ProxyPlayerHD/65816_SBC_v1/KiCad/65C816_SBC.kicad_sch

## KiCad design KiCad/65C816_SBC.kicad_sch (2022-10-29)

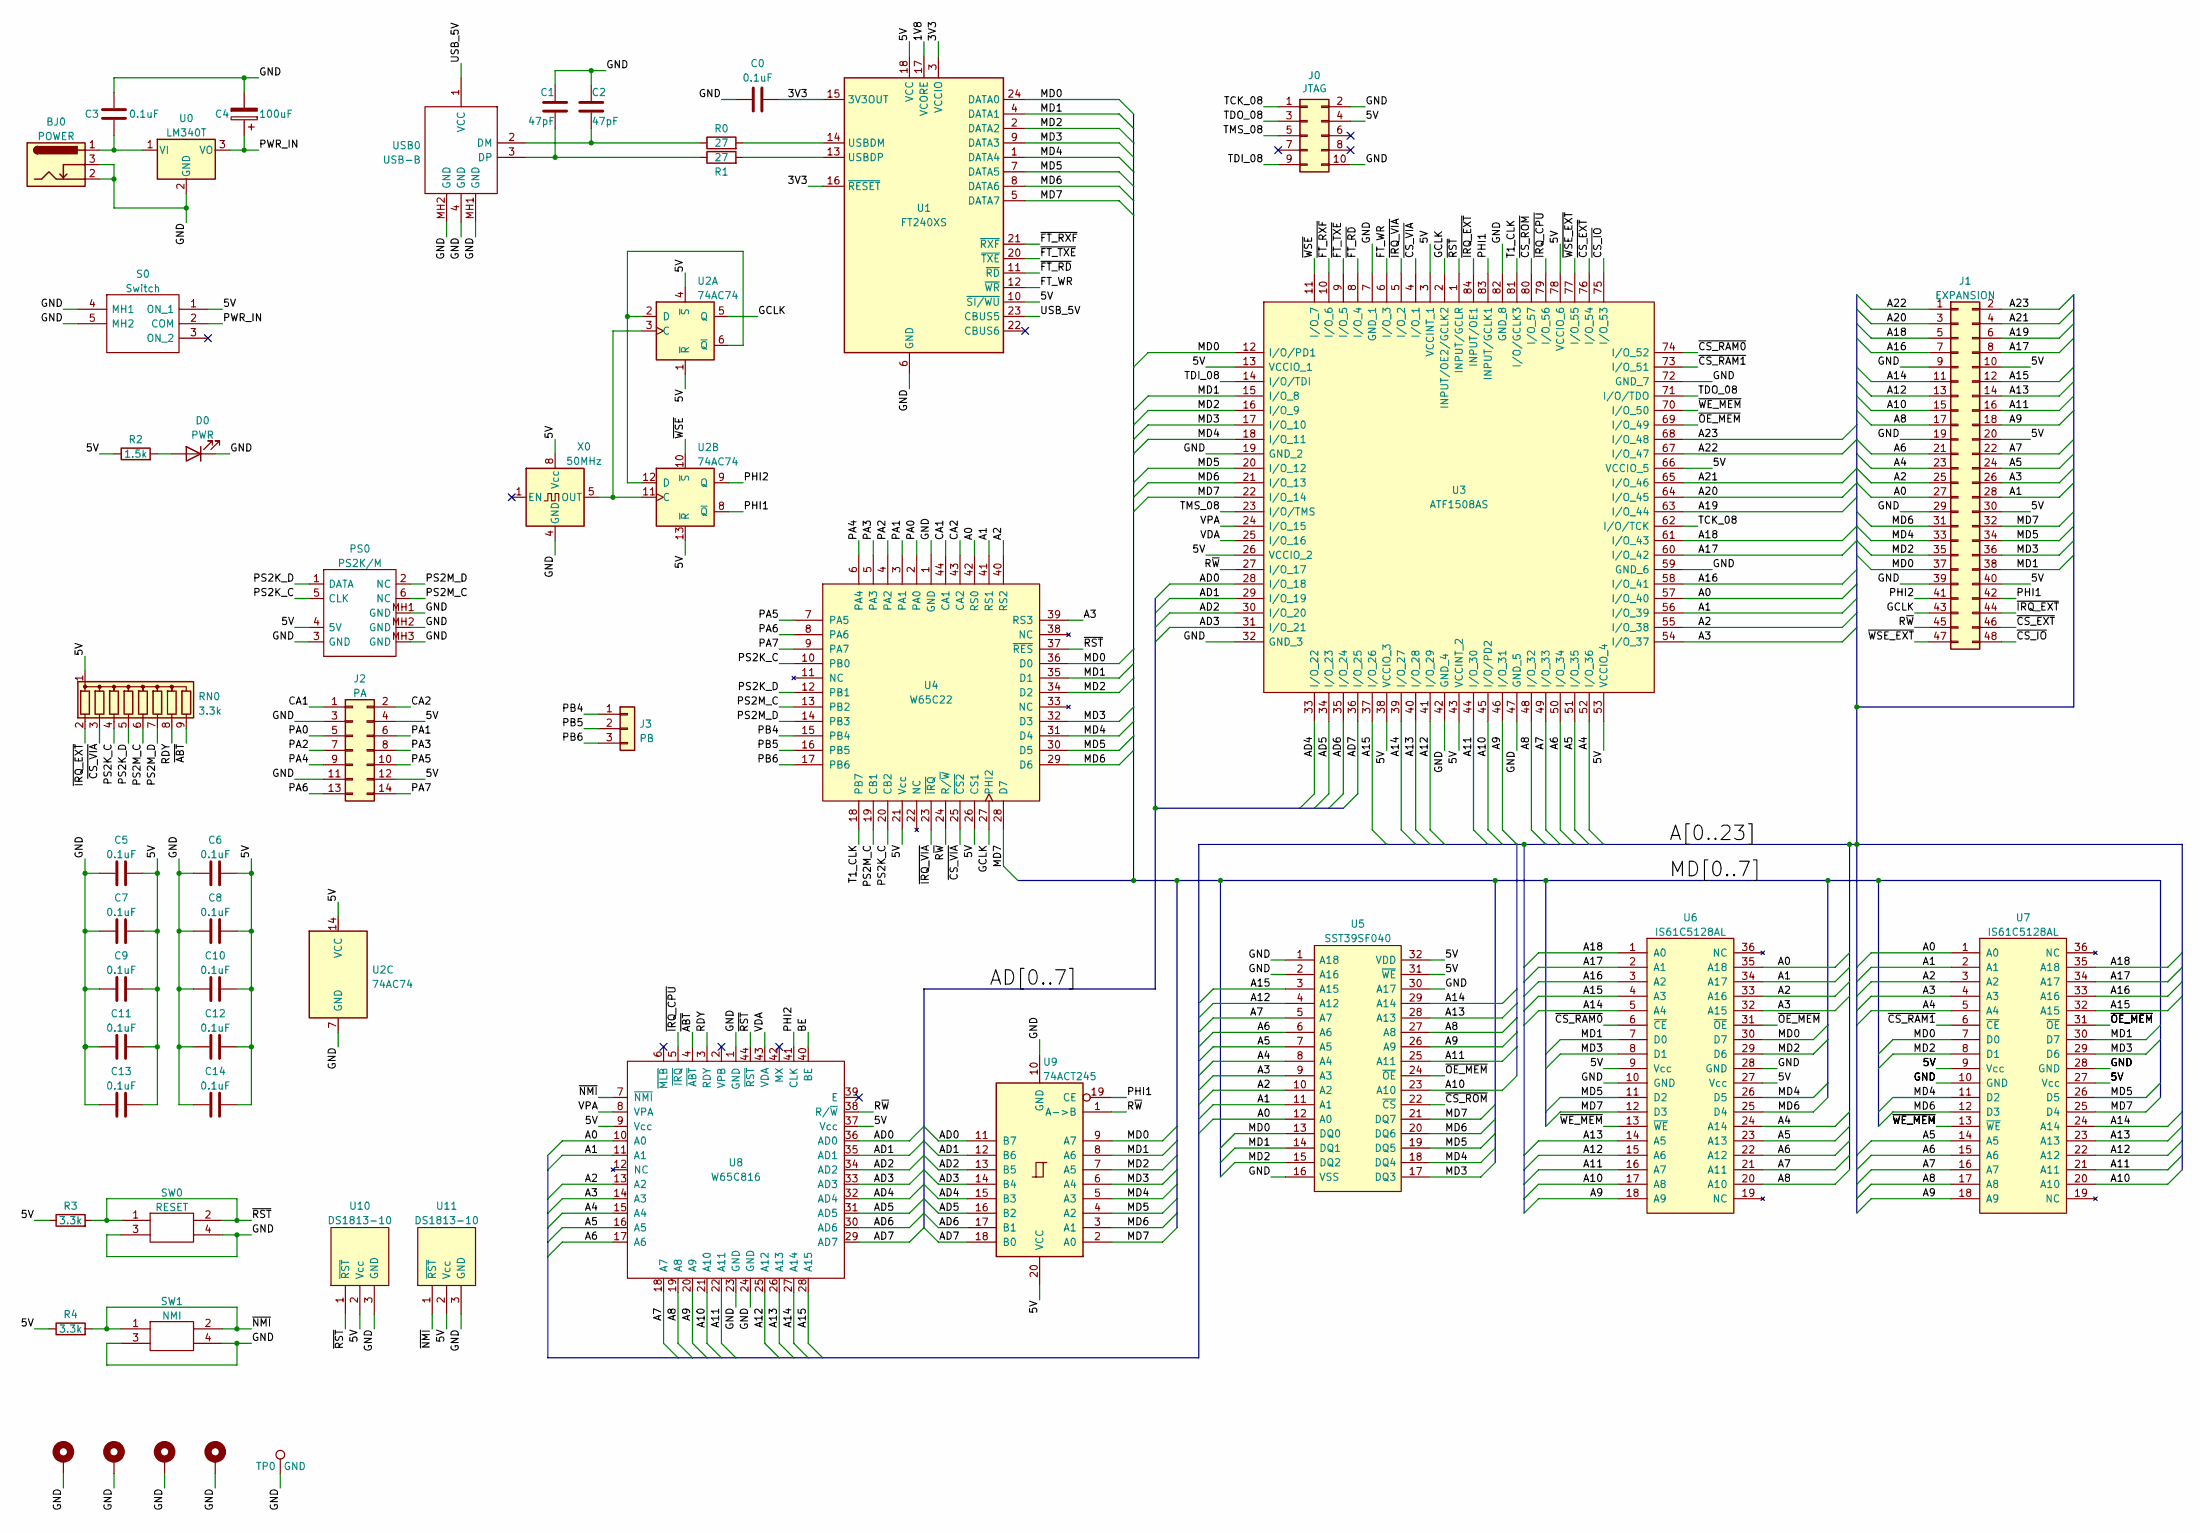
[picture p2: schematic 65C816_SBC.kicad_sch]

Parts:
BJ0: POWER; BarrelJack_Horizontal
C0, C3, C5, C6, C7, C8, C9, C10, C11, C12, C13, C14: 0.1uF; C_Disc_D4.3mm_W1.9mm_P5.00mm
C1, C2: 47pF; C_Disc_D4.3mm_W1.9mm_P5.00mm
C4: 100uF; CP_Radial_D4.0mm_P2.00mm
D0: PWR; LED_D4.0mm
H0, H1, H2, H3: H; MountingHole_3.2mm_M3_Pad
J0: JTAG; PinHeader_2x05_P2.54mm_Vertical
J1: EXPANSION; PinHeader_2x24_P2.54mm_Vertical
J2: PA; PinHeader_2x07_P2.54mm_Vertical
J3: PB; PinHeader_1x03_P2.54mm_Vertical
PS0: PS2K/M; PS2; Mouser Part Number 571-5749266-1
R0, R1: 27; R_Axial_DIN0207_L6.3mm_D2.5mm_P2.54mm_Vertical
R2: 1.5k; R_Axial_DIN0207_L6.3mm_D2.5mm_P2.54mm_Vertical
R3, R4: 3.3k; R_Axial_DIN0207_L6.3mm_D2.5mm_P2.54mm_Vertical
RN0: 3.3k; R_Array_SIP9
S0: Switch; Mouser Part Number 688-SSSF012100
SW0: RESET; button
SW1: NMI; button
TP0: GND; TestPoint_Bridge_Pitch5.08mm_Drill1.3mm
U0: LM340T; TO-220-3_Vertical
U1: FT240XS; SSOP-24_3.9x8.7mm_P0.635mm
U2: 74AC74; DIP-14_W7.62mm_Socket
U3: ATF1508AS; PLCC-84_THT-Socket
U4: W65C22; PLCC-44_THT-Socket
U5: SST39SF040; PLCC-32_THT-Socket
U6, U7: IS61C5128AL; SOJ-36_10.16x23.49mm_P1.27mm
U8: W65C816; PLCC-44_THT-Socket
U9: 74ACT245; DIP-20_W7.62mm_Socket
U10, U11: DS1813-10; TO-92L_Inline_Wide
USB0: USB-B; Mouser Part Number 523-UE27-BC54-130
X0: 50MHz; Oscillator_DIP-8

Connections:
1V8: U1.17 (VCORE)
3V3: C0.1, U1.3 (VCCIO), U1.15 (3V3OUT), U1.16 (~RESET)
5V: C5.2, C6.2, C7.2, C8.2, C9.2, C10.2, C11.2, C12.2, C13.2, C14.2, J0.4, J1.10, J1.20, J1.30, J1.40, J2.4, J2.12, PS0.4 (5V), R2.1, R3.1, R4.1, RN0.1 (common), S0.1 (ON_1), U1.10 (~SI/WU), U1.18 (VCC), U2.1 (~R), U2.4 (~S), U2.13 (~R), U2.14 (VCC), U3.3 (VCCINT_1), U3.13 (VCCIO_1), U3.26 (VCCIO_2), U3.38 (VCCIO_3), U3.43 (VCCINT_2), U3.53 (VCCIO_4), U3.66 (VCCIO_5), U3.78 (VCCIO_6), U4.21 (Vcc), U4.26 (CS1), U5.31 (~WE), U5.32 (VDD), U6.9 (Vcc), U6.27 (Vcc), U7.9 (Vcc), U7.27 (Vcc), U8.9 (Vcc), U8.37 (Vcc), U9.20 (VCC), U10.2 (Vcc), U11.2 (Vcc), X0.8 (Vcc)
A0: J1.27, U3.57 (I/O_40), U4.42 (RS0), U5.12 (A0), U6.35 (A18), U7.1 (A0), U8.10 (A0)
A1: J1.28, U3.56 (I/O_39), U4.41 (RS1), U5.11 (A1), U6.34 (A17), U7.2 (A1), U8.11 (A1)
A2: J1.25, U3.55 (I/O_38), U4.40 (RS2), U5.10 (A2), U6.33 (A16), U7.3 (A2), U8.13 (A2)
A3: J1.26, U3.54 (I/O_37), U4.39 (RS3), U5.9 (A3), U6.32 (A15), U7.4 (A3), U8.14 (A3)
A4: J1.23, U3.52 (I/O_36), U5.8 (A4), U6.24 (A14), U7.5 (A4), U8.15 (A4)
A5: J1.24, U3.51 (I/O_35), U5.7 (A5), U6.23 (A13), U7.14 (A5), U8.16 (A5)
A6: J1.21, U3.50 (I/O_34), U5.6 (A6), U6.22 (A12), U7.15 (A6), U8.17 (A6)
A7: J1.22, U3.49 (I/O_33), U5.5 (A7), U6.21 (A11), U7.16 (A7), U8.18 (A7)
A8: J1.17, U3.48 (I/O_32), U5.27 (A8), U6.20 (A10), U7.17 (A8), U8.19 (A8)
A9: J1.18, U3.46 (I/O_31), U5.26 (A9), U6.18 (A9), U7.18 (A9), U8.20 (A9)
A10: J1.15, U3.45 (I/O/PD2), U5.23 (A10), U6.17 (A8), U7.20 (A10), U8.21 (A10)
A11: J1.16, U3.44 (I/O_30), U5.25 (A11), U6.16 (A7), U7.21 (A11), U8.22 (A11)
A12: J1.13, U3.41 (I/O_29), U5.4 (A12), U6.15 (A6), U7.22 (A12), U8.25 (A12)
A13: J1.14, U3.40 (I/O_28), U5.28 (A13), U6.14 (A5), U7.23 (A13), U8.26 (A13)
A14: J1.11, U3.39 (I/O_27), U5.29 (A14), U6.5 (A4), U7.24 (A14), U8.27 (A14)
A15: J1.12, U3.37 (I/O_26), U5.3 (A15), U6.4 (A3), U7.32 (A15), U8.28 (A15)
A16: J1.7, U3.58 (I/O_41), U6.3 (A2), U7.33 (A16)
A17: J1.8, U3.60 (I/O_42), U6.2 (A1), U7.34 (A17)
A18: J1.5, U3.61 (I/O_43), U6.1 (A0), U7.35 (A18)
A19: J1.6, U3.63 (I/O_44)
A20: J1.3, U3.64 (I/O_45)
A21: J1.4, U3.65 (I/O_46)
A22: J1.1, U3.67 (I/O_47)
A23: J1.2, U3.68 (I/O_48)
AD0: U3.28 (I/O_18), U8.36 (AD0), U9.11 (B7)
AD1: U3.29 (I/O_19), U8.35 (AD1), U9.12 (B6)
AD2: U3.30 (I/O_20), U8.34 (AD2), U9.13 (B5)
AD3: U3.31 (I/O_21), U8.33 (AD3), U9.14 (B4)
AD4: U3.33 (I/O_22), U8.32 (AD4), U9.15 (B3)
AD5: U3.34 (I/O_23), U8.31 (AD5), U9.16 (B2)
AD6: U3.35 (I/O_24), U8.30 (AD6), U9.17 (B1)
AD7: U3.36 (I/O_25), U8.29 (AD7), U9.18 (B0)
BE: U8.40 (BE)
CA1: J2.1, U4.44 (CA1)
CA2: J2.2, U4.43 (CA2)
FT_WR: U1.12 (~WR), U3.6 (I/O_3)
GCLK: J1.43, U2.5 (Q), U3.2 (INPUT/OE2/GCLK2), U4.27 (PHI2)
GND: BJ0.2, BJ0.3, C0.2, C1.2, C2.1, C3.2, C4.2, C5.1, C6.1, C7.1, C8.1, C9.1, C10.1, C11.1, C12.1, C13.1, C14.1, D0.1 (K), H0.1, H1.1, H2.1, H3.1, J0.2, J0.10, J1.9, J1.19, J1.29, J1.39, J2.3, J2.11, PS0.3 (GND), PS0.MH1 (GND), PS0.MH2 (GND), PS0.MH3 (GND), S0.4 (MH1), S0.5 (MH2), SW0.3, SW0.4, SW1.3, SW1.4, TP0.1, U0.2 (GND), U1.6 (GND), U1.19 (GND), U2.7 (GND), U3.7 (GND_1), U3.19 (GND_2), U3.32 (GND_3), U3.42 (GND_4), U3.47 (GND_5), U3.59 (GND_6), U3.72 (GND_7), U3.82 (GND_8), U4.1 (GND), U5.1 (A18), U5.2 (A16), U5.16 (VSS), U5.30 (A17), U6.10 (GND), U6.28 (GND), U7.10 (GND), U7.28 (GND), U8.1 (GND), U8.23 (GND), U8.24 (GND), U9.10 (GND), U10.3 (GND), U11.3 (GND), USB0.4 (GND), USB0.MH1 (GND), USB0.MH2 (GND), X0.4 (GND)
MD0: J1.37, U1.24 (DATA0), U3.12 (I/O/PD1), U4.36 (D0), U5.13 (DQ0), U6.30 (D7), U7.7 (D0), U9.9 (A7)
MD1: J1.38, U1.4 (DATA1), U3.15 (I/O_8), U4.35 (D1), U5.14 (DQ1), U6.7 (D0), U7.30 (D7), U9.8 (A6)
MD2: J1.35, U1.2 (DATA2), U3.16 (I/O_9), U4.34 (D2), U5.15 (DQ2), U6.29 (D6), U7.8 (D1), U9.7 (A5)
MD3: J1.36, U1.9 (DATA3), U3.17 (I/O_10), U4.32 (D3), U5.17 (DQ3), U6.8 (D1), U7.29 (D6), U9.6 (A4)
MD4: J1.33, U1.1 (DATA4), U3.18 (I/O_11), U4.31 (D4), U5.18 (DQ4), U6.26 (D5), U7.11 (D2), U9.5 (A3)
MD5: J1.34, U1.7 (DATA5), U3.20 (I/O_12), U4.30 (D5), U5.19 (DQ5), U6.11 (D2), U7.26 (D5), U9.4 (A2)
MD6: J1.31, U1.8 (DATA6), U3.21 (I/O_13), U4.29 (D6), U5.20 (DQ6), U6.25 (D4), U7.12 (D3), U9.3 (A1)
MD7: J1.32, U1.5 (DATA7), U3.22 (I/O_14), U4.28 (D7), U5.21 (DQ7), U6.12 (D3), U7.25 (D4), U9.2 (A0)
unnamed: BJ0.1, C3.1, U0.1 (VI)
unnamed: C1.1, R1.1, USB0.3 (DP)
unnamed: C2.2, R0.1, USB0.2 (DM)
unnamed: D0.2 (A), R2.2
unnamed: R0.2, U1.14 (USBDM)
unnamed: R1.2, U1.13 (USBDP)
unnamed: U2.3 (C), U2.11 (C), X0.5 (OUT)
unnamed: U2.2 (D), U2.6 (~Q), U2.12 (D)
PA0: J2.5, U4.2 (PA0)
PA1: J2.6, U4.3 (PA1)
PA2: J2.7, U4.4 (PA2)
PA3: J2.8, U4.5 (PA3)
PA4: J2.9, U4.6 (PA4)
PA5: J2.10, U4.7 (PA5)
PA6: J2.13, U4.8 (PA6)
PA7: J2.14, U4.9 (PA7)
PB4: J3.1, U4.15 (PB4)
PB5: J3.2, U4.16 (PB5)
PB6: J3.3, U4.17 (PB6)
PHI1: J1.42, U2.8 (~Q), U3.83 (INPUT/GCLK1), U9.19 (CE)
PHI2: J1.41, U2.9 (Q), U8.41 (CLK)
PS2K_C: PS0.5 (CLK), RN0.4 (R3), U4.10 (PB0), U4.20 (CB2)
PS2K_D: PS0.1 (DATA), RN0.5 (R4), U4.12 (PB1)
PS2M_C: PS0.6 (NC), RN0.6 (R5), U4.13 (PB2), U4.19 (CB1)
PS2M_D: PS0.2 (NC), RN0.7 (R6), U4.14 (PB3)
PWR_IN: C4.1, S0.2 (COM), U0.3 (VO)
RDY: RN0.8 (R7), U8.3 (RDY)
R~W: J1.45, U3.27 (I/O_17), U4.24 (R/~W), U8.38 (R/~W), U9.1 (A->B)
T1_CLK: U3.81 (I/O/GCLK3), U4.18 (PB7)
TCK_08: J0.1, U3.62 (I/O/TCK)
TDI_08: J0.9, U3.14 (I/O/TDI)
TDO_08: J0.3, U3.71 (I/O/TDO)
TMS_08: J0.5, U3.23 (I/O/TMS)
USB_5V: U1.23 (CBUS5), USB0.1 (VCC)
VDA: U3.25 (I/O_16), U8.43 (VDA)
VPA: U3.24 (I/O_15), U8.8 (VPA)
~ABT: RN0.9 (R8), U8.4 (~ABT)
~CS_EXT: J1.46, U3.76 (I/O_54)
~CS_IO: J1.48, U3.75 (I/O_53)
~CS_RAM0: U3.74 (I/O_52), U6.6 (~CE)
~CS_RAM1: U3.73 (I/O_51), U7.6 (~CE)
~CS_ROM: U3.80 (I/O_57), U5.22 (~CS)
~CS_VIA: RN0.3 (R2), U3.4 (I/O_1), U4.25 (~CS2)
~FT_RD: U1.11 (~RD), U3.8 (I/O_4)
~FT_RXF: U1.21 (~RXF), U3.10 (I/O_6)
~FT_TXE: U1.20 (~TXE), U3.9 (I/O_5)
~IRQ_CPU: U3.79 (I/O_56), U8.5 (~IRQ)
~IRQ_EXT: J1.44, RN0.2 (R1), U3.84 (INPUT/OE1)
~IRQ_VIA: U3.5 (I/O_2), U4.23 (~IRQ)
~NMI: R4.2, SW1.1, SW1.2, U8.7 (~NMI), U11.1 (~RST)
~OE_MEM: U3.69 (I/O_49), U5.24 (~OE), U6.31 (~OE), U7.31 (~OE)
~RST: R3.2, SW0.1, SW0.2, U3.1 (INPUT/GCLR), U4.37 (~RES), U8.44 (~RST), U10.1 (~RST)
~WE_MEM: U3.70 (I/O_50), U6.13 (~WE), U7.13 (~WE)
~WSE_EXT: J1.47, U3.77 (I/O_55)
~WSE: U2.10 (~S), U3.11 (I/O_7)
